miguelangelcasanova/codos/dev/esp8266/codos_WeMos_D1_Mini_Pro/codos_WeMos_D1_Mini_Pro_interior.JPG

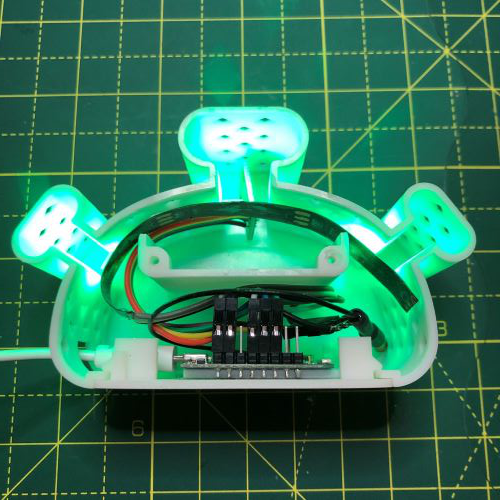
dev/esp8266/codos_WeMos_D1_Mini_Pro/codos_WeMos_D1_Mini_Pro_interior.JPG
