miguelangelcasanova/codos/img/photo_2020-09-19_11-16-08.jpg

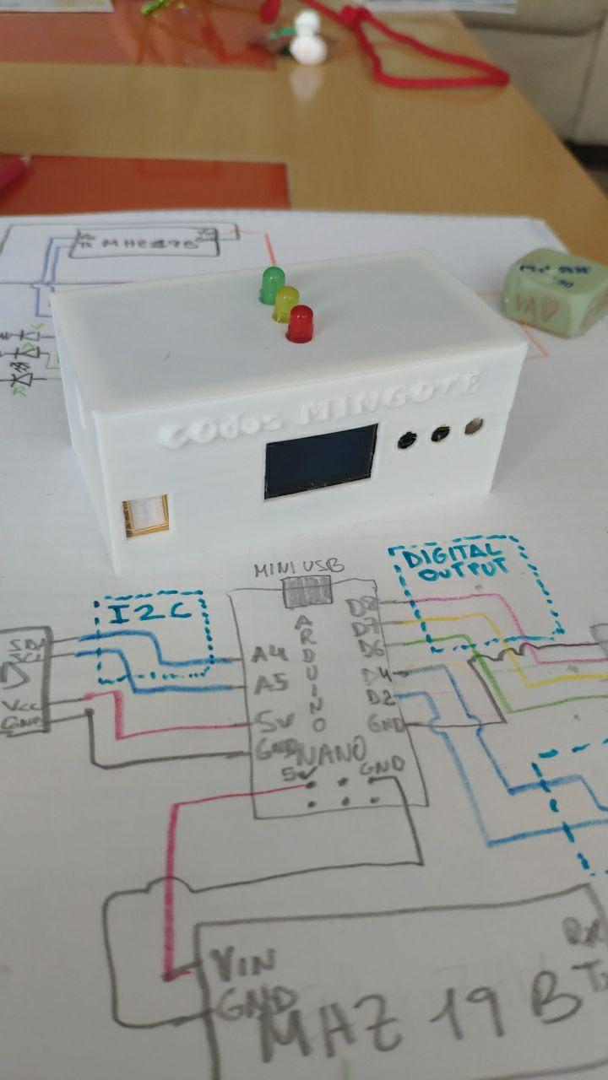
img/photo_2020-09-19_11-16-08.jpg
