miguelangelcasanova/codos/src/codos.ino

/*********************************************************************************
CODOS AKA CO2 
Un sistema de bajo coste basado en ESP32 para la detección del CO2 
y otras variables ambientales para monitorizar la calidad del aire en el aula
(o en otros lugares de trabajo)
*********************************************************************************/

#include "Wire.h"                       // Librería Wire para el soporte del protocolo i2c
#include "WiFi.h"                       // Librería Wi-Fi
#include <Adafruit_BME280.h>            // Librería para el sensor BME280
#include <Adafruit_Sensor.h>            // Librería estándar para los sensores de Adafruit
#include <SparkFunCCS811.h>             // Puedes descargar la librería para el sensor de CO2 en: http://librarymanager/All#SparkFun_CCS811


#define CO2_sensor_present true         // Debe seleccionarse si este sensor está o no presente
#define BME280_sensor_present true      // Debe seleccionarse si este sensor está o no presente
#define OLED_present false              // Debe seleccionarse si la pantalla está o no presente
#define traffic_lights_present true     // Debe seleccionarse si se conectará el semáforo o no (el sensor de CO2 debe estar presente también en ese caso)

#define CCS811_ADDR 0x5A                // Dirección i2c del sensor de CO2
//#define CCS811_ADDR 0x5B                // Dirección i2c alternativa del sensor de CO2

CCS811 CO2_sensor(CCS811_ADDR);   
long int CO2_value;

const int CO2_safe_level = 2000;        // Se debe especificar un valor máximo de CO2 seguro
const int CO2_alarm_level = 3000;       // Se debe especificar un valor máximo de CO2 de alarma 

#define BME280_ADDR 0x76                // Dirección i2c del sensor BME280

Adafruit_BME280 BME280_sensor;          // Dirección i2c del sensor de humedad, presión y temperatura

#define verde 23
#define amarillo 18
#define rojo 13

// Reemplaza los datos con el identificador de la red WIFI y la contraseña del aula
//const char* ssid     = "NOMBRE_DE_TU_RED";
//const char* password = "CLAVE_DE_TU_RED";

WiFiServer server(80);                  // Seleccionar el puerto del servidor Web

// Variable to store the HTTP request
String header;

// Current time
unsigned long currentTime = millis();
// Previous time
unsigned long previousTime = 0; 
// Define timeout time in milliseconds (example: 2000ms = 2s)
const long timeoutTime = 2000;

bool blink = true;

void setup() {
  Serial.begin(115200);
  bool status;

  Serial.println("Sensores CCS811 y BME280");

  Wire.begin(); //Inialize I2C Hardware
  
  if (CO2_sensor_present){
    if (CO2_sensor.begin() == false)
    {
      Serial.print("Error: el sensor de CO2 CCS811 no se encuentra. Por favor, comprueba el cableado.");
      while (1)
        ;
    }
  }  
  if (BME280_sensor_present){
    delay(10);  
    if (!BME280_sensor.begin(BME280_ADDR)) {
      Serial.println("Error: el sensor de temperatura, presión y humedad BME280 no se encuentra. Por favor, comprueba el cableado.");
      while (1);
    }
  }

  pinMode(verde, OUTPUT);
  pinMode(amarillo, OUTPUT);
  pinMode(rojo, OUTPUT);  
  // Apagar los led al empezar
  digitalWrite(verde, LOW);
  digitalWrite(amarillo, LOW);
  digitalWrite(rojo, LOW);

  // Conectar a la red  Wi-Fi con el SSID y la contraseña selecionadas
  Serial.print("Conectando a ");
  Serial.println(ssid);
  WiFi.begin(ssid, password);
  while (WiFi.status() != WL_CONNECTED) {
    delay(500);
    Serial.print(".");
  }
  // Print local IP address and start web server
  Serial.println("");
  Serial.println("WiFi conectada.");
  Serial.println("Dirección IP del servidor: ");
  Serial.println(WiFi.localIP());
  server.begin();
  
  // initialize digital pin LED_BUILTIN as an output.
  pinMode(LED_BUILTIN, OUTPUT);
}

void loop(){
  blink=!blink;
  digitalWrite(LED_BUILTIN,blink);   // turn the LED on (HIGH is the voltage level)
  WiFiClient client = server.available();   // Listen for incoming clients

  if (client) {                             // If a new client connects,
    currentTime = millis();
    previousTime = currentTime;
    Serial.println("Nuevo cliente conectado.");          // print a message out in the serial port
    String currentLine = "";                // make a String to hold incoming data from the client
    while (client.connected() && currentTime - previousTime <= timeoutTime) {  // loop while the client's connected
      currentTime = millis();
      if (client.available()) {             // if there's bytes to read from the client,
        char c = client.read();             // read a byte, then
        Serial.write(c);                    // print it out the serial monitor
        header += c;
        if (c == '\n') {                    // if the byte is a newline character
          // if the current line is blank, you got two newline characters in a row.
          // that's the end of the client HTTP request, so send a response:
          if (currentLine.length() == 0) {
            // HTTP headers always start with a response code (e.g. HTTP/1.1 200 OK)
            // and a content-type so the client knows what's coming, then a blank line:
            client.println("HTTP/1.1 200 OK");
            client.println("Content-type:text/html");
            client.println("Connection: close");
            client.println();
            
            // Display the HTML web page
            client.println("<!DOCTYPE html><html>");
            // Web Page Heading
            client.println("<head><meta name=\"viewport\" content=\"width=device-width, initial-scale=1\">");
            client.println("<link rel=\"icon\" href=\"data:,\">");
            // CSS to style the table 
            client.println("<style>body { text-align: center; font-family: \"Trebuchet MS\", Arial;}");
            client.println("table { border-collapse: collapse; width:35%; margin-left:auto; margin-right:auto; }");
            client.println("th { padding: 12px; background-color: #0043af; color: white; }");
            client.println("tr { border: 1px solid #ddd; padding: 12px; }");
            client.println("tr:hover { background-color: #bcbcbc; }");
            client.println("td { border: none; padding: 12px; }");
            client.println(".sensor { color:blue; font-weight: bold; background-color: #ffffff; padding: 1px; }");
            client.println("</style>");
            client.println("<meta http-equiv=\"refresh\" content=\"1\">");
            client.println("</head>");
            // Web Page Body
            client.println("<body><h1>&#128170;CODOS&#128170;</h1>");
            client.println("<p>Sistema de medida de la calidad del aire y otros par&#225;metros ambientales del aula</p>");
            client.println("<table><tr><th>Medida</th><th>Valor</th></tr>");
            if (BME280_sensor_present){
              client.println("<tr><td>Temp. Celsius</td><td><span class=\"sensor\">");
              client.println(BME280_sensor.readTemperature());
              client.println(" &#176;C</span></td></tr>");  
              client.println("<tr><td>Presi&#243;n</td><td><span class=\"sensor\">");
              client.println(BME280_sensor.readPressure() / 100.0F);
              client.println(" hPa</span></td></tr>");
              client.println("<tr><td>Humedad</td><td><span class=\"sensor\">");
              client.println(BME280_sensor.readHumidity());
              client.println(" %</span></td></tr>"); 
            }
            if (CO2_sensor_present){
              if (CO2_sensor.dataAvailable()){            
                CO2_sensor.readAlgorithmResults();
                client.println("<tr><td>eCO<sub>2</sub></td><td><span class=\"sensor\">");
                client.println(CO2_sensor.getCO2());
                client.println(" ppm</span></td></tr>"); 
                traffic_lights();
                client.println("<tr><td>TVOC</td><td><span class=\"sensor\">");
                client.println(CO2_sensor.getTVOC());
                client.println(" ppb</span></td></tr>"); 
              }
            }
            client.println("</table>");
            client.println("<br/><br/>");
            client.println("<a href='https://es.wikipedia.org/wiki/CO2_equivalente' target='_blank'>&#191;Qu&#233; es el eCO<sub>2</sub>?</a> ");
            client.println("<a href='https://es.wikipedia.org/wiki/Compuestos_org%C3%A1nicos_vol%C3%A1tiles' target='_blank'>&#191;Qu&#233; significa TVOC?</a>");
            client.println("</body></html>");
            // The HTTP response ends with another blank line
            client.println();
            // Break out of the while loop
            break;
          } 
          else { // if you got a newline, then clear currentLine
            currentLine = "";
          }
        } else if (c != '\r') {  // if you got anything else but a carriage return character,
          currentLine += c;      // add it to the end of the currentLine
        }
      }
    }
    // Clear the header variable
    header = "";
    // Close the connection
    client.stop();
    Serial.println("Client disconnected.");
    Serial.println("");
  }
  delay(2000);
}

void traffic_lights(){
  CO2_sensor.readAlgorithmResults();
  CO2_value = CO2_sensor.getCO2();
  Serial.println(CO2_value);
  if (CO2_value <= CO2_safe_level){
    // Encender el led verde y apagar el resto
    Serial.println("Parece que el aula no necesita más ventilación de momento");
    digitalWrite(verde, HIGH);
    digitalWrite(amarillo, LOW);
    digitalWrite(rojo, LOW);
  } 
  if ((CO2_value > CO2_safe_level) & (CO2_value < CO2_alarm_level)) {
    // Encender el led amarillo y apagar el resto
    Serial.println("El aire del aula necesitará renovarse pronto");
    digitalWrite(verde, LOW);
    digitalWrite(amarillo, HIGH);
    digitalWrite(rojo, LOW);
  }
  if (CO2_value >= CO2_alarm_level){
    // Encender el led rojo y apagar el resto
    Serial.println("Habría que ventilar el aula");
    digitalWrite(verde, LOW);
    digitalWrite(amarillo, LOW);
    digitalWrite(rojo, HIGH);
  }
}
