miguelangelcasanova/codos/dev/esp8266/gauge/gauge.ino

/*
Versión gráfica con gauges para mostrar los valores de los sensores usando ESP8266 SPIFFS HTML Web Page with JPEG, PNG Image 
a partir de un ejemplo de https://circuits4you.com
*/

#include <ESP8266WiFi.h>
#include <ESP8266WebServer.h>
#include <ESP8266mDNS.h>
#include <FS.h>   //Include File System Headers

const char* htmlfile = "/index.html";

//WiFi Connection configuration
//const char *ssid = "NOMBRE_DE_TU_RED_WIFI";
//const char *password = "CLAVE_DE_TU_RED_WIFI";

ESP8266WebServer server(80);

void handleeCO2(){
  long int eCO2_value = 400;
  String eCO2 = String(eCO2_value);
  Serial.println(eCO2);
  server.send(200, "text/plane",eCO2);
}

void handleTVOC(){
  long int TVOC_value = 0;
  String TVOC = String(TVOC_value);
  Serial.println(TVOC);
  server.send(200, "text/plane",TVOC);
}

void handleRoot(){
  server.sendHeader("Location", "/index.html",true);   //Redirect to our html web page
  server.send(302, "text/plane","");
}

void handleWebRequests(){
  if(loadFromSpiffs(server.uri())) return;
  String message = "File Not Detected\n\n";
  message += "URI: ";
  message += server.uri();
  message += "\nMethod: ";
  message += (server.method() == HTTP_GET)?"GET":"POST";
  message += "\nArguments: ";
  message += server.args();
  message += "\n";
  for (uint8_t i=0; i<server.args(); i++){
    message += " NAME:"+server.argName(i) + "\n VALUE:" + server.arg(i) + "\n";
  }
  server.send(404, "text/plain", message);
  Serial.println(message);
}

void setup() {
  delay(1000);
  Serial.begin(115200);
  Serial.println();

  //Initialize File System
  SPIFFS.begin();
  Serial.println("Inicializando el sistema de archivos");

  
  //Connect to wifi Network
  WiFi.begin(ssid, password);     //Connect to your WiFi router
  Serial.println("Conectando a la red WiFi");

  // Wait for connection
  while (WiFi.status() != WL_CONNECTED) {
    delay(500);
    Serial.print(".");
  }

  //If connection successful show IP address in serial monitor
  Serial.println("");
  Serial.print("Conectado a ");
  Serial.println(ssid);
  Serial.print("Dirección IP del dispositivo: ");
  Serial.println(WiFi.localIP());  //IP address assigned to your ESP

  //Start mDNS
  if (MDNS.begin("aula001")) { 
    Serial.println("mDNS started");
  }

  //Initialize Webserver
  server.on("/",handleRoot);
  server.on("/geteCO2",handleeCO2); //Reads eCO2 function is called from out index.html
  server.on("/getTVOC",handleTVOC); //Reads TVOC function is called from out index.html
  server.onNotFound(handleWebRequests); //Set setver all paths are not found so we can handle as per URI
  server.begin();  
}

void loop() {
 server.handleClient();
}

bool loadFromSpiffs(String path){
  String dataType = "text/plain";
  if(path.endsWith("/")) path += "index.htm";

  if(path.endsWith(".src")) path = path.substring(0, path.lastIndexOf("."));
  else if(path.endsWith(".html")) dataType = "text/html";
  else if(path.endsWith(".htm")) dataType = "text/html";
  else if(path.endsWith(".css")) dataType = "text/css";
  else if(path.endsWith(".js")) dataType = "application/javascript";
  else if(path.endsWith(".png")) dataType = "image/png";
  else if(path.endsWith(".gif")) dataType = "image/gif";
  else if(path.endsWith(".jpg")) dataType = "image/jpeg";
  else if(path.endsWith(".ico")) dataType = "image/x-icon";
  else if(path.endsWith(".xml")) dataType = "text/xml";
  else if(path.endsWith(".pdf")) dataType = "application/pdf";
  else if(path.endsWith(".zip")) dataType = "application/zip";
  File dataFile = SPIFFS.open(path.c_str(), "r");
  if (server.hasArg("download")) dataType = "application/octet-stream";
  if (server.streamFile(dataFile, dataType) != dataFile.size()) {
  }

  dataFile.close();
  return true;
}
